bitfieldlabs/afm_saucer/afm_saucer_atmega328p/src/led.c

/***********************************************************************
 *    _   _   _             _     __                                           
 *   /_\ | |_| |_ __ _  ___| | __/ _|_ __ ___  _ __ ___   /\/\   __ _ _ __ ___ 
 *  //_\\| __| __/ _` |/ __| |/ / |_| '__/ _ \| '_ ` _ \ /    \ / _` | '__/ __|
 * /  _  \ |_| || (_| | (__|   <|  _| | | (_) | | | | | / /\/\ \ (_| | |  \__ \
 * \_/ \_/\__|\__\__,_|\___|_|\_\_| |_|  \___/|_| |_| |_\/    \/\__,_|_|  |___/
 *
 *                              ____ ____ ___ 
 *                              |--< |__, |==]
 *
 *                      ____ ____ _  _ ____ ____ ____
 *                      ==== |--| |__| |___ |=== |--<
 *
 *  Copyright (c) 2022 bitfield labs
 * 
 ***********************************************************************
 *  This file is part of the Attack from Mars! RGB saucer project:
 *  https://github.com/bitfieldlabs/afm_saucer
 *
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
 *  You should have received a copy of the GNU Lesser General Public
 *  License along with afterglow.
 *  If not, see <http://www.gnu.org/licenses/>.
 ***********************************************************************/

#include "led.h"
#include <avr/interrupt.h>


// Code by josh.com
// https://wp.josh.com/2014/05/13/ws2812-neopixels-are-not-so-finicky-once-you-get-to-know-them/


//------------------------------------------------------------------------------
// definitions

#define PIXEL_PORT0  PORTD  // Port of the pin the pixels are connected to
#define PIXEL_BIT0   5      // Bit of the pin the pixels are connected to

#define PIXEL_PORT1  PORTD  // Port of the pin the pixels are connected to
#define PIXEL_BIT1   6      // Bit of the pin the pixels are connected to

// These are the timing constraints taken mostly from the WS2812 datasheets 
// These are chosen to be conservative and avoid problems rather than for maximum throughput 

#define T1H  900    // Width of a 1 bit in ns
#define T1L  600    // Width of a 1 bit in ns

#define T0H  400    // Width of a 0 bit in ns
#define T0L  900    // Width of a 0 bit in ns

// Older pixels would reliabily reset with a 6us delay, but some newer (>2019) ones
// need 250us. This is set to the longer delay here to make sure things work, but if
// you want to get maximum refresh speed, you can try decreasing this until your pixels
// start to flicker. 

#define RES 250000    // Width of the low gap between bits to cause a frame to latch

// Here are some convience defines for using nanoseconds specs to generate actual CPU delays

#define NS_PER_SEC (1000000000L)          // Note that this has to be SIGNED since we want to be able to check for negative values of derivatives

#define CYCLES_PER_SEC (F_CPU)

#define NS_PER_CYCLE ( NS_PER_SEC / CYCLES_PER_SEC )

#define NS_TO_CYCLES(n) ( (n) / NS_PER_CYCLE )


//------------------------------------------------------------------------------
void sendBit0(bool bitVal) {
  
    if (bitVal)
    {
		asm volatile (
			"sbi %[port], %[bit] \n\t"				// Set the output bit
			".rept %[onCycles] \n\t"                                // Execute NOPs to delay exactly the specified number of cycles
			"nop \n\t"
			".endr \n\t"
			"cbi %[port], %[bit] \n\t"                              // Clear the output bit
			".rept %[offCycles] \n\t"                               // Execute NOPs to delay exactly the specified number of cycles
			"nop \n\t"
			".endr \n\t"
			::
			[port]		"I" (_SFR_IO_ADDR(PIXEL_PORT0)),
			[bit]		"I" (PIXEL_BIT0),
			[onCycles]	"I" (NS_TO_CYCLES(T1H) - 2),		// 1-bit width less overhead  for the actual bit setting, note that this delay could be longer and everything would still work
			[offCycles] 	"I" (NS_TO_CYCLES(T1L) - 2)			// Minimum interbit delay. Note that we probably don't need this at all since the loop overhead will be enough, but here for correctness

		);
    }
    else
    {
    	// **************************************************************************
		// This line is really the only tight goldilocks timing in the whole program!
		// **************************************************************************

        cli();
		asm volatile (
			"sbi %[port], %[bit] \n\t"				// Set the output bit
			".rept %[onCycles] \n\t"				// Now timing actually matters. The 0-bit must be long enough to be detected but not too long or it will be a 1-bit
			"nop \n\t"                                              // Execute NOPs to delay exactly the specified number of cycles
			".endr \n\t"
			"cbi %[port], %[bit] \n\t"                              // Clear the output bit
			".rept %[offCycles] \n\t"                               // Execute NOPs to delay exactly the specified number of cycles
			"nop \n\t"
			".endr \n\t"
			::
			[port]		"I" (_SFR_IO_ADDR(PIXEL_PORT0)),
			[bit]		"I" (PIXEL_BIT0),
			[onCycles]	"I" (NS_TO_CYCLES(T0H) - 2),
			[offCycles]	"I" (NS_TO_CYCLES(T0L) - 2)

		);
        sei();
    }
    
    // Note that the inter-bit gap can be as long as you want as long as it doesn't exceed the 5us reset timeout (which is A long time)
    // Here I have been generous and not tried to squeeze the gap tight but instead erred on the side of lots of extra time.
    // This has thenice side effect of avoid glitches on very long strings becuase 
}

//------------------------------------------------------------------------------
void sendBit1(bool bitVal) {
  
    if (bitVal)
    {
		asm volatile (
			"sbi %[port], %[bit] \n\t"				// Set the output bit
			".rept %[onCycles] \n\t"                                // Execute NOPs to delay exactly the specified number of cycles
			"nop \n\t"
			".endr \n\t"
			"cbi %[port], %[bit] \n\t"                              // Clear the output bit
			".rept %[offCycles] \n\t"                               // Execute NOPs to delay exactly the specified number of cycles
			"nop \n\t"
			".endr \n\t"
			::
			[port]		"I" (_SFR_IO_ADDR(PIXEL_PORT1)),
			[bit]		"I" (PIXEL_BIT1),
			[onCycles]	"I" (NS_TO_CYCLES(T1H) - 2),		// 1-bit width less overhead  for the actual bit setting, note that this delay could be longer and everything would still work
			[offCycles] 	"I" (NS_TO_CYCLES(T1L) - 2)			// Minimum interbit delay. Note that we probably don't need this at all since the loop overhead will be enough, but here for correctness

		);
    }
    else
    {
    	// **************************************************************************
		// This line is really the only tight goldilocks timing in the whole program!
		// **************************************************************************

        cli();
		asm volatile (
			"sbi %[port], %[bit] \n\t"				// Set the output bit
			".rept %[onCycles] \n\t"				// Now timing actually matters. The 0-bit must be long enough to be detected but not too long or it will be a 1-bit
			"nop \n\t"                                              // Execute NOPs to delay exactly the specified number of cycles
			".endr \n\t"
			"cbi %[port], %[bit] \n\t"                              // Clear the output bit
			".rept %[offCycles] \n\t"                               // Execute NOPs to delay exactly the specified number of cycles
			"nop \n\t"
			".endr \n\t"
			::
			[port]		"I" (_SFR_IO_ADDR(PIXEL_PORT1)),
			[bit]		"I" (PIXEL_BIT1),
			[onCycles]	"I" (NS_TO_CYCLES(T0H) - 2),
			[offCycles]	"I" (NS_TO_CYCLES(T0L) - 2)

		);
        sei();
    }
    
    // Note that the inter-bit gap can be as long as you want as long as it doesn't exceed the 5us reset timeout (which is A long time)
    // Here I have been generous and not tried to squeeze the gap tight but instead erred on the side of lots of extra time.
    // This has thenice side effect of avoid glitches on very long strings becuase 
}

//------------------------------------------------------------------------------ 
void sendByte(uint8_t byte, bool firstString)
{
    for (uint8_t bit = 0; bit < 8; bit++)
    {
        if (firstString)
        {
            sendBit0(byte & 0x80);
        }
        else
        {
            sendBit1(byte & 0x80);
        }
                                                        // so send highest bit (bit #7 in an 8-bit byte since they start at 0)
        byte <<= 1;                                    // and then shift left so bit 6 moves into 7, 5 moves into 6, etc     
    }           
} 

//------------------------------------------------------------------------------
void sendPixel(uint8_t r, uint8_t g, uint8_t b, bool firstString)
{  
    sendByte(r, firstString);
    sendByte(g, firstString);
    sendByte(b, firstString);
}
